liveboxandy/ZX-Max-128-Issue-3/Step/CONN_5-520315-8_TYC.stp

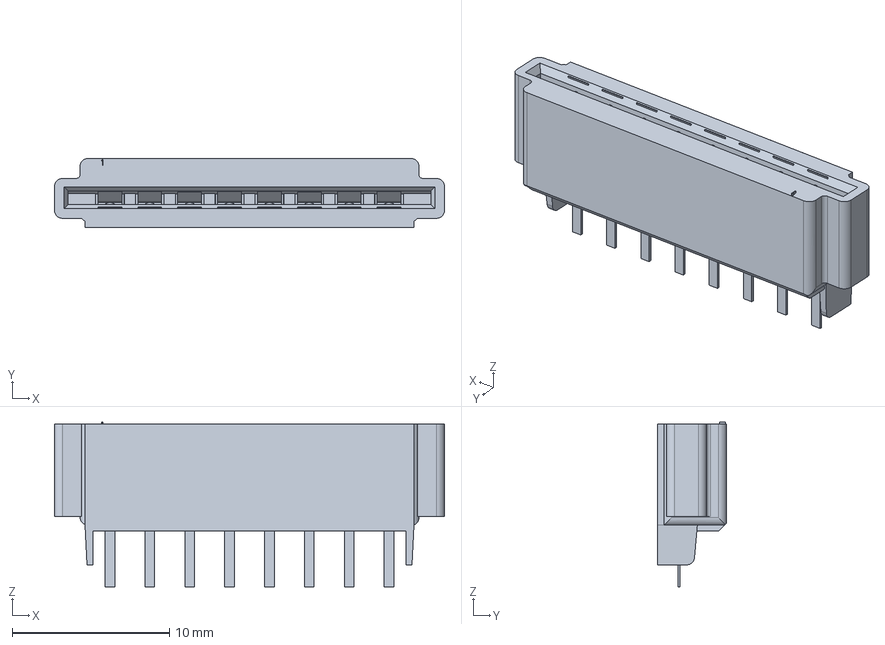
[picture p17: CAD file, 2026-07-10]
Step/CONN_5-520315-8_TYC.stp
24.8 x 4.39 x 10.5 mm
