liveboxandy/ZX-Max-128-Issue-3/Step/ESP8266-12E_ESP-12E.step

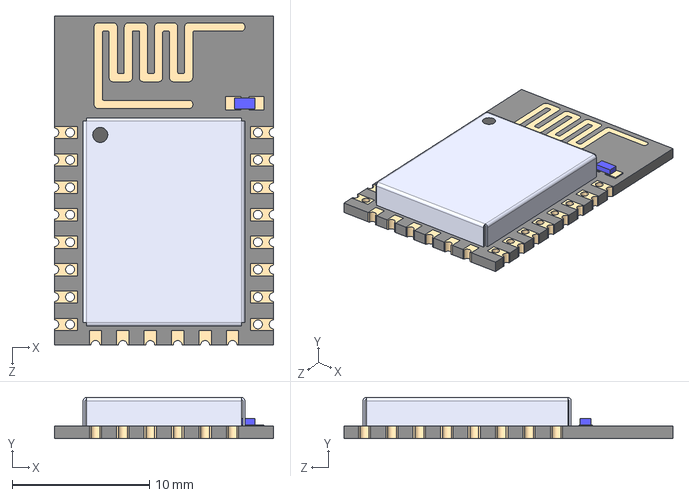
[picture p18: CAD file, 2026-07-10]
Step/ESP8266-12E_ESP-12E.step
16.0 x 3.00 x 24.0 mm
