liveboxandy/ZX-Max-128-Issue-3/Step/DIP-14_W7.62mm_Socket.step

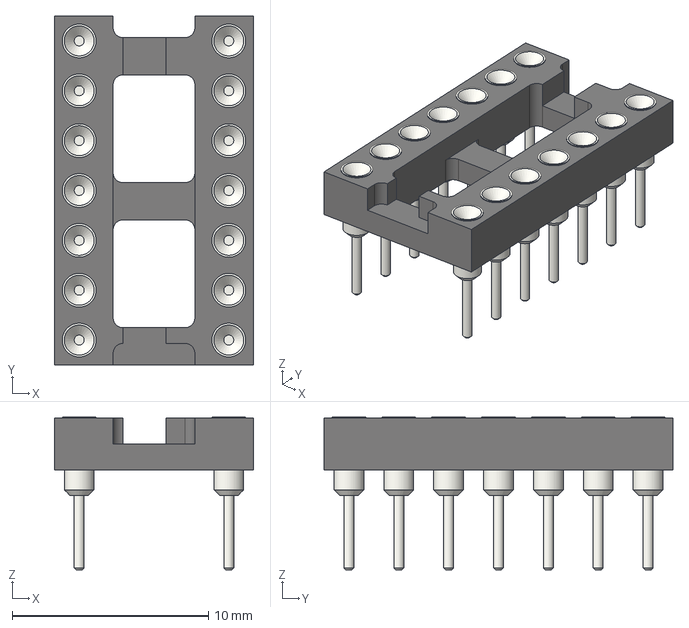
[picture p20: CAD file, 2026-07-10]
Step/DIP-14_W7.62mm_Socket.step
10.2 x 17.8 x 7.79 mm
