liveboxandy/ZX-Max-128-Issue-3/Step/DF02M.stp

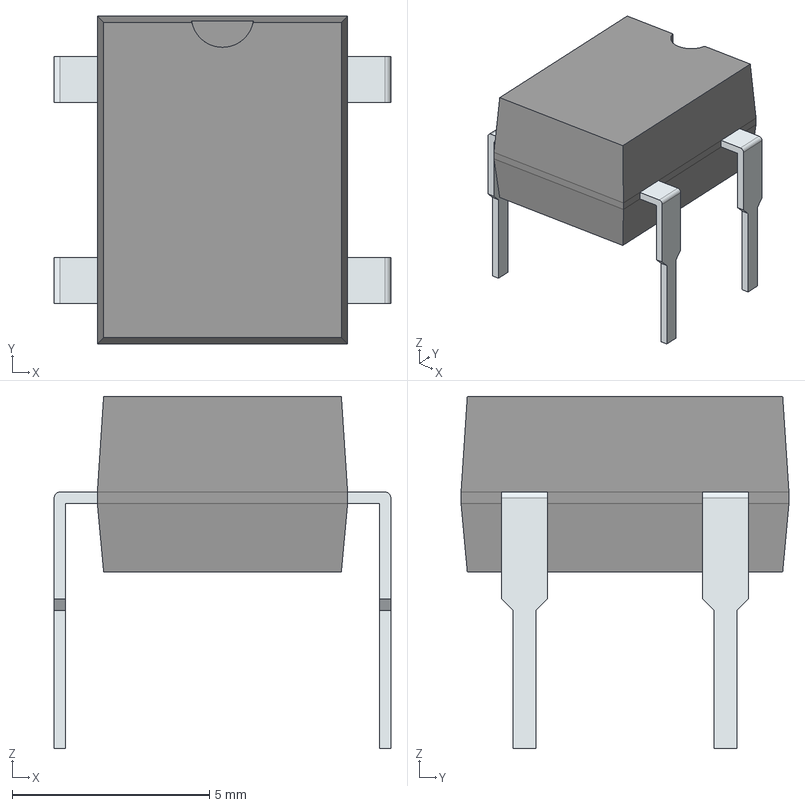
[picture p21: CAD file, 2026-07-10]
Step/DF02M.stp
8.54 x 8.32 x 8.93 mm
PinsArrayLR
