liveboxandy/ZX-Max-128-Issue-3/Step/PJ-322.step

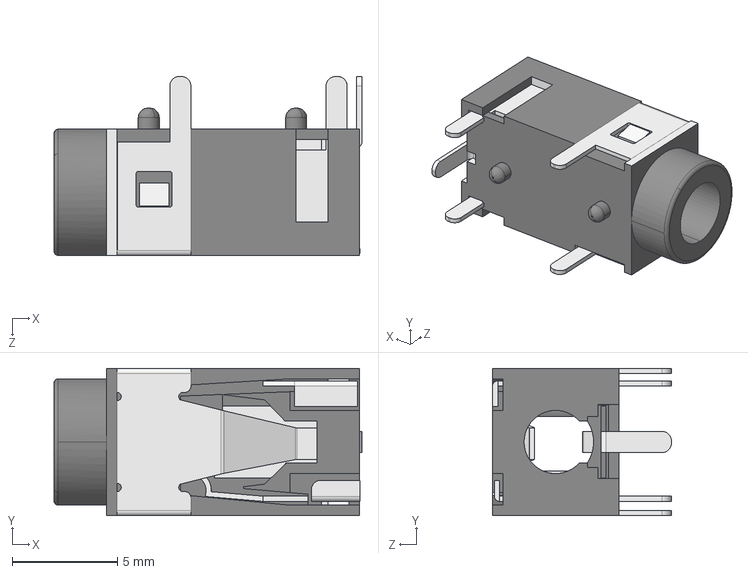
[picture p23: CAD file, 2026-07-10]
Step/PJ-322.step
14.6 x 7.00 x 8.50 mm
