liveboxandy/ZX-Max-128-Issue-3/Step/Capacitor 100pF 50V MLCC K101J15C0GF53L2.stp

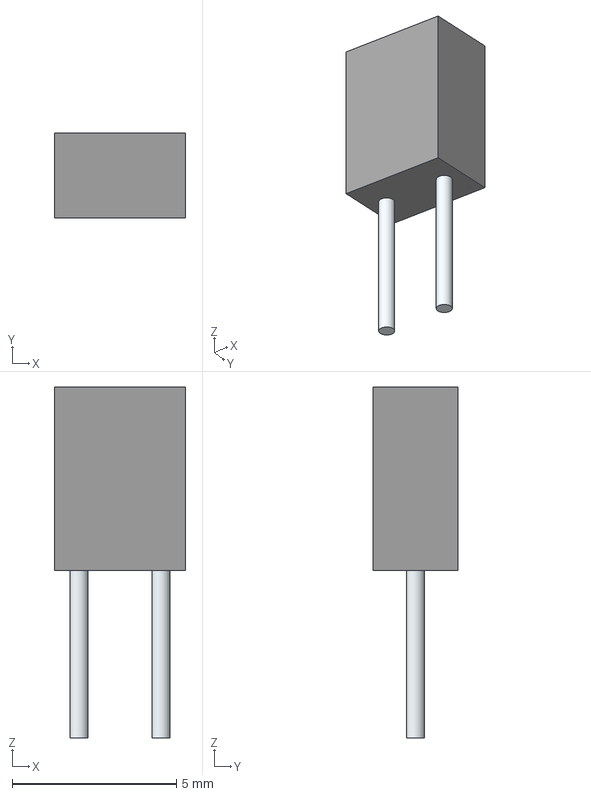
[picture p26: CAD file, 2026-07-10]
Step/Capacitor 100pF 50V MLCC K101J15C0GF53L2.stp
4.00 x 2.60 x 10.7 mm
Leads x 2
