liveboxandy/ZX-Max-128-Issue-3/Step/PLCC-84-AT.stp

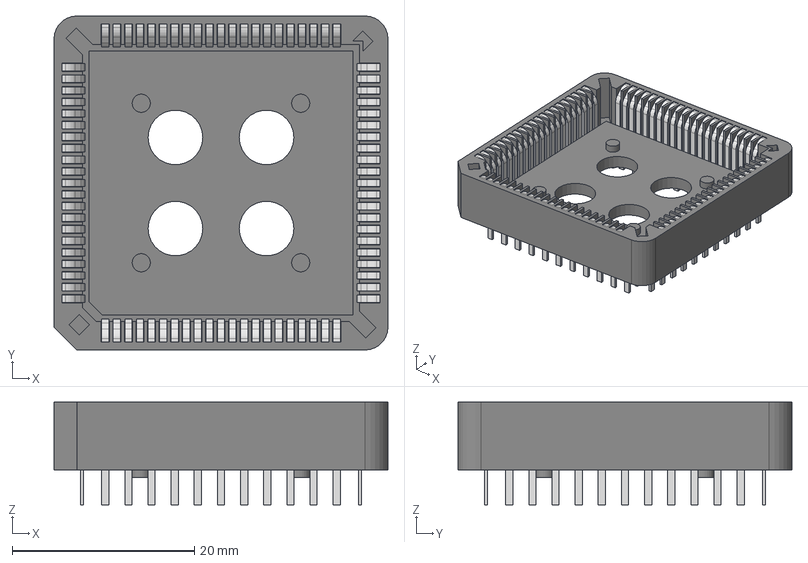
[picture p27: CAD file, 2026-07-10]
Step/PLCC-84-AT.stp
36.7 x 36.7 x 11.3 mm
