liveboxandy/ZX-Max-128-Issue-3/Step/DIP-28_W15.24mm_Socket.step

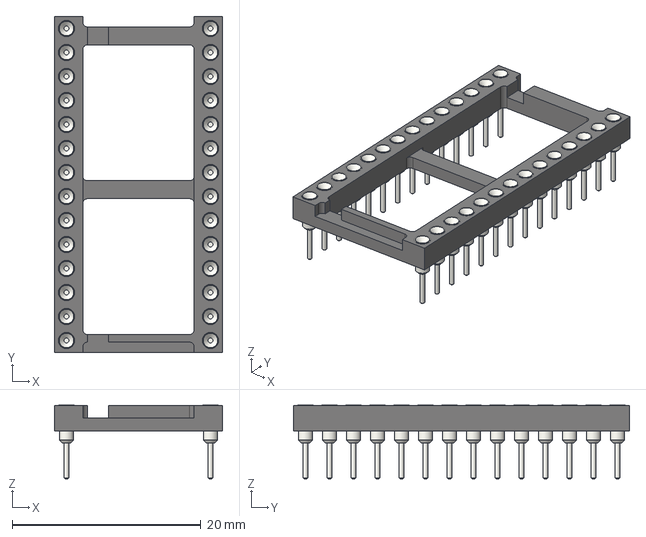
[picture p29: CAD file, 2026-07-10]
Step/DIP-28_W15.24mm_Socket.step
17.8 x 35.6 x 7.79 mm
