liveboxandy/ZX-Max-128-Issue-3/Step/Header 5x2 Pin-Pin 10129381-906002BLF.step

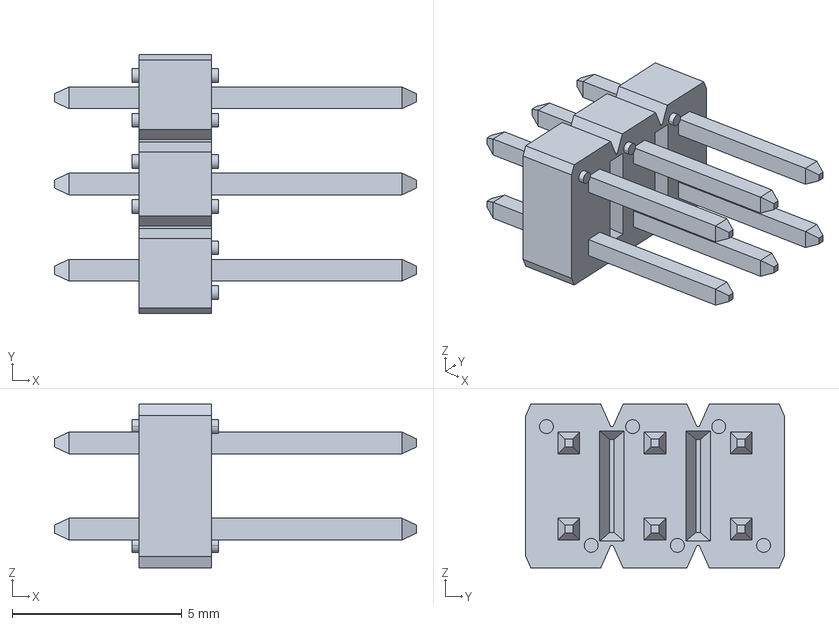
[picture p33: CAD file, 2026-07-10]
Step/Header 5x2 Pin-Pin 10129381-906002BLF.step
10.7 x 7.62 x 4.83 mm
