liveboxandy/ZX-Max-128-Issue-3/Step/ADI724JRZ RW_16_ADI.step

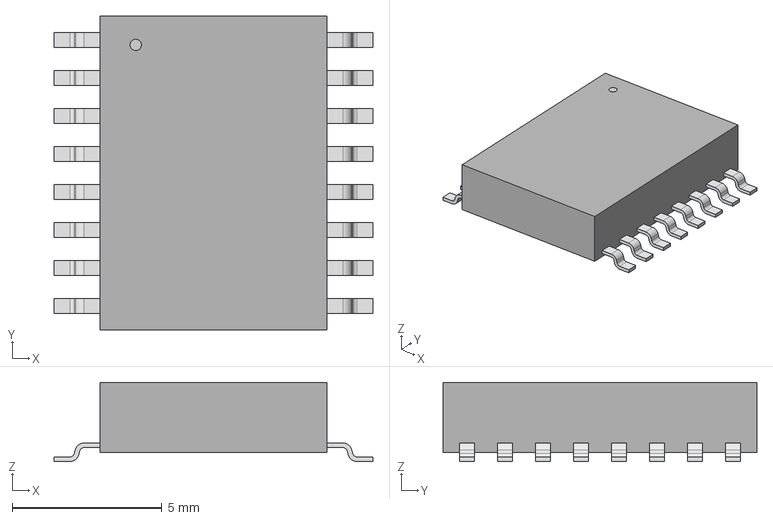
[picture p34: CAD file, 2026-07-10]
Step/ADI724JRZ RW_16_ADI.step
10.6 x 10.5 x 2.64 mm
