liveboxandy/ZX-Max-128-Issue-3/Step/Capacitor 22uF 16V 5x7 EEAGA1C220H.step

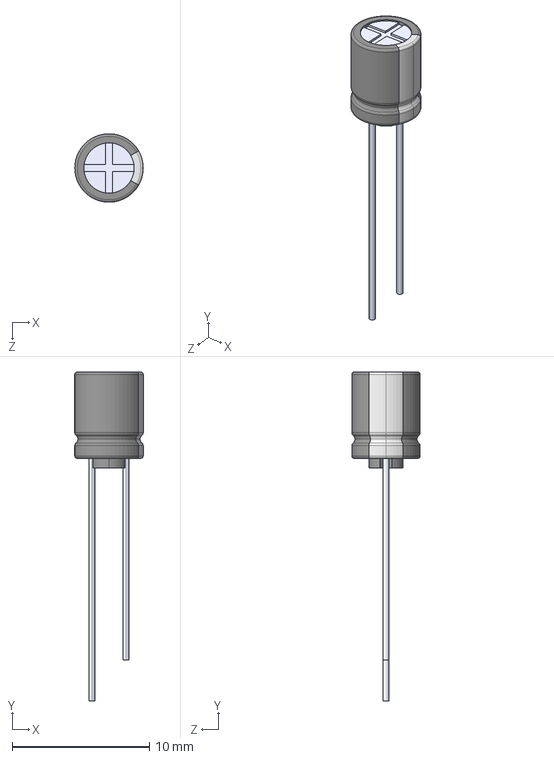
[picture p41: CAD file, 2026-07-10]
Step/Capacitor 22uF 16V 5x7 EEAGA1C220H.step
5.00 x 24.0 x 4.99 mm
