liveboxandy/ZX-Max-128-Issue-3/Step/DIP-32_W15.24mm_Socket.step

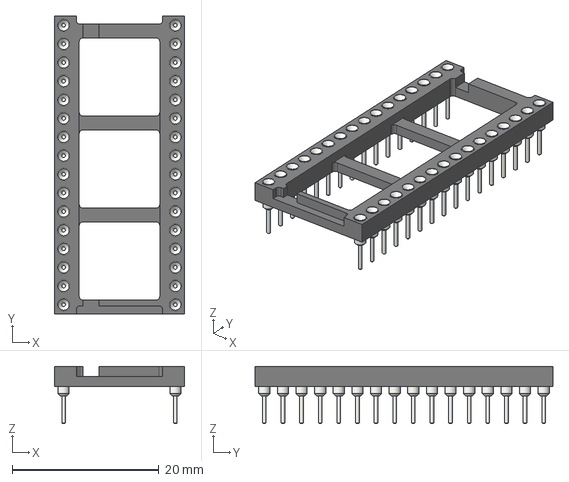
[picture p42: CAD file, 2026-07-10]
Step/DIP-32_W15.24mm_Socket.step
17.8 x 40.6 x 7.79 mm
